Neusaap128/Super-Epische-Audio-Generator/SEAG_F/Core/Inc/main.h

#define ShiftRegFDat_Pin GPIO_PIN_13
#define ShiftRegFDat_GPIO_Port GPIOC
#define ShiftRegFStoClk_Pin GPIO_PIN_14
#define ShiftRegFStoClk_GPIO_Port GPIOC
#define ShiftRegFClk_Pin GPIO_PIN_15
#define ShiftRegFClk_GPIO_Port GPIOC
#define ShiftRegLBarDat_Pin GPIO_PIN_0
#define ShiftRegLBarDat_GPIO_Port GPIOC
#define ShiftRegLBarStoClk_Pin GPIO_PIN_2
#define ShiftRegLBarStoClk_GPIO_Port GPIOC
#define ShiftRegLBarClk_Pin GPIO_PIN_3
#define ShiftRegLBarClk_GPIO_Port GPIOC
#define RotEncoderInA_Pin GPIO_PIN_6
#define RotEncoderInA_GPIO_Port GPIOC
#define RotEncoderInA_EXTI_IRQn EXTI9_5_IRQn
#define RotEncoderInB_Pin GPIO_PIN_7
#define RotEncoderInB_GPIO_Port GPIOC
#define RotEncoderInB_EXTI_IRQn EXTI9_5_IRQn
#define RotEncoderButton_Pin GPIO_PIN_8
#define RotEncoderButton_GPIO_Port GPIOC
#define RotEncoderButton_EXTI_IRQn EXTI9_5_IRQn
#define ToggleInput4_Pin GPIO_PIN_9
#define ToggleInput4_GPIO_Port GPIOA
#define ToggleInput3_Pin GPIO_PIN_10
#define ToggleInput3_GPIO_Port GPIOA
#define ToggleInput2_Pin GPIO_PIN_11
#define ToggleInput2_GPIO_Port GPIOA
#define ToggleInput1_Pin GPIO_PIN_12
#define ToggleInput1_GPIO_Port GPIOA
#define ToggleInput8_Pin GPIO_PIN_15
#define ToggleInput8_GPIO_Port GPIOA
#define ToggleInput7_Pin GPIO_PIN_10
#define ToggleInput7_GPIO_Port GPIOC
#define ToggleInput6_Pin GPIO_PIN_11
#define ToggleInput6_GPIO_Port GPIOC
#define ToggleInput5_Pin GPIO_PIN_12
#define ToggleInput5_GPIO_Port GPIOC
