Neusaap128/Super-Epische-Audio-Generator/SEAG_F/Core/Inc/IO/IO.c

/*
 * IO.c
 *
 *  Created on: Mar 23, 2024
 *      Author: rode-
 */

#define bitset(byte,nbit)   ((byte) |=  (1<<(nbit)))
#define bitclear(byte,nbit) ((byte) &= ~(1<<(nbit)))

#include "IO.h"
#include "RotaryEncoder.h"

//het defineeren van alle pinnen van shift register filter
ShiftRegister_t shiftRegFilterSelect = {
	.clkPort 	 = ShiftRegFClk_GPIO_Port,
	.clkPin   	 = ShiftRegFClk_Pin,
	.dataPort 	 = ShiftRegFDat_GPIO_Port,
	.dataPin  	 = ShiftRegFDat_Pin,
	.enabledPort = ShiftRegFStoClk_GPIO_Port,
	.enabledPin  = ShiftRegFStoClk_Pin
};

//het defineren van alle pinnen voor de ledbar
ShiftRegister_t shiftRegLedbar = {
	.clkPort 	 = ShiftRegLBarClk_GPIO_Port,
	.clkPin   	 = ShiftRegLBarClk_Pin,
	.dataPort 	 = ShiftRegLBarDat_GPIO_Port,
	.dataPin  	 = ShiftRegLBarDat_Pin,
	.enabledPort = ShiftRegLBarStoClk_GPIO_Port,
	.enabledPin  = ShiftRegLBarStoClk_Pin
};
//het defineren van pinnen voor de rotaryEncoder
RotaryEncoder_t rotaryEncoder = {
	.currentPos	= 0,
	.portA   	= RotEncoderInA_GPIO_Port,
	.pinA 	 	= RotEncoderInA_Pin,
	.portB  	= RotEncoderInB_GPIO_Port,
	.pinB 		= RotEncoderInB_Pin,
	.portButton = RotEncoderButton_GPIO_Port,
	.pinButton  = RotEncoderButton_Pin
};


IOState_t IOState;

uint8_t selectedFilter;

// 0 no state transition
// 1, SelectingValue -> Disabled
// 2, Disabled -> SelectingFilter
// 3, SelectingFilter -> SelectingValue
uint8_t switchedStateFlag;

void InitIO(){
	LoadValueIntoShiftRegister(&shiftRegFilterSelect, 0x00);
	ResetShiftRegister(&shiftRegLedbar);
}

void HandleSelectingFilter(){

	selectedFilter = (uint16_t)(rotaryEncoder.currentPos/4) % AMOUNT_OF_FILTERS; //door dat rotery de 4 fase overloopt en 4 keer opteld of afteld moet je delen door 4, voor varable extra dat weergeeft hoeveel filters er zijn
	LoadValueIntoShiftRegister(&shiftRegFilterSelect, 1 << selectedFilter);

}

void HandleSelectingValue(){

	uint8_t led_bar = (rotaryEncoder.currentPos/4); //door dat rotery de 4 fase overloopt en 4 keer opteld of afteld moet je delen door 4
	uint8_t ledbar_array = (1 << led_bar) - 1;		//we werken binair dus hierdoor deze shift opperatie

	changeFilterLevel(getFilters()->filterInstances[selectedFilter], (float)led_bar/(8-1));

	LoadValueIntoShiftRegister(&shiftRegLedbar, ledbar_array);

}

//de functie die moet opgeroepen worden als er op de knop drukt
void ButtonInterrupt(){

	IOState = (IOState + 1)%3;

	rotaryEncoder.currentPos = 0;

	switchedStateFlag = IOState + 1;


}
//op roepen als er aan de knop gedraaid word
void RotaryEncoderInterrupt(){
	rot_intrupt(&rotaryEncoder);
}

uint8_t newSelectedFilters = 0b00000000;
void IOUpdate(){


	uint8_t buttonPressed = HAL_GPIO_ReadPin(ToggleInput1_GPIO_Port, ToggleInput1_Pin);
	if( !buttonPressed) newSelectedFilters |= (1 << 0);  else newSelectedFilters &= ~(1 << 0); // inverted because toggle is upside down
	buttonPressed = HAL_GPIO_ReadPin(ToggleInput2_GPIO_Port, ToggleInput2_Pin);
	if( buttonPressed) newSelectedFilters |= (1 << 1);  else newSelectedFilters &= ~(1 << 1);
	buttonPressed = HAL_GPIO_ReadPin(ToggleInput3_GPIO_Port, ToggleInput3_Pin);
	if( buttonPressed) newSelectedFilters |= (1 << 2);  else newSelectedFilters &= ~(1 << 2);
	buttonPressed = HAL_GPIO_ReadPin(ToggleInput4_GPIO_Port, ToggleInput4_Pin);
	if(!buttonPressed) newSelectedFilters |= (1 << 3);  else newSelectedFilters &= ~(1 << 3); // inverted because toggle is upside down
	buttonPressed = HAL_GPIO_ReadPin(ToggleInput5_GPIO_Port, ToggleInput5_Pin);
	if( buttonPressed) newSelectedFilters |= (1 << 4);  else newSelectedFilters &= ~(1 << 4);



	/*
	uint8_t buttonPressed = HAL_GPIO_ReadPin(ToggleInput6_GPIO_Port, ToggleInput6_Pin);
	SetFilterState(5, buttonPressed);
	uint8_t buttonPressed = HAL_GPIO_ReadPin(ToggleInput7_GPIO_Port, ToggleInput7_Pin);
	SetFilterState(6, buttonPressed);
	uint8_t buttonPressed = HAL_GPIO_ReadPin(ToggleInput8_GPIO_Port, ToggleInput8_Pin);
	SetFilterState(7, buttonPressed);
	 */

	if(newSelectedFilters != GetEnabledFilters()){
		UpdateLedsActiveFilters();
	}

	//Handling Transistions
	if(switchedStateFlag > 0){

		switch(switchedStateFlag){
			case 1:
				LoadValueIntoShiftRegister(&shiftRegFilterSelect, GetEnabledFilters());
				ResetShiftRegister(&shiftRegLedbar);
				break;
			case 2:
				// Nothing needs to be reset
				break;
			case 3:
				// Nothing needs to be reset
				rotaryEncoder.currentPos = 4; // At least one led on, at start
				break;
		}

		switchedStateFlag = 0;

	}

	//Handling states
	switch (IOState) {
	    case Disabled:
	    	break;
	    case SelectingFilter:			//deze fase gaat er een filter dat je wilt aanpassen geselecteerd
	    	HandleSelectingFilter();
	    	break;
	    case SelectingValue:			//hier ga je van de geselecteerde filter de waarde gaan aanpassen
	    	HandleSelectingValue();
	    	break;
	  }

}

void UpdateLedsActiveFilters(){

	SetFilterStates(newSelectedFilters);
	LoadValueIntoShiftRegister(&shiftRegFilterSelect, GetEnabledFilters());

}
