Neusaap128/Super-Epische-Audio-Generator/CubeIDEProject/Core/Inc/DSP/DSP.h

/*
 * DSP.h
 *
 *  Created on: Feb 25, 2024
 *      Author: Joran
 */

#ifndef INC_DSP_DSP_H_
#define INC_DSP_DSP_H_

#define AMOUNT_OF_FILTERS 4

#include "stm32g4xx_hal.h"
#include <string.h>
#include <stdio.h>
#include <stdint.h>
#include <stdlib.h>
#include "../Filters/MovingAverage.h"

typedef uint32_t SampleType;

extern const int N;
extern const int samplingRate;

void InitDSP();
void AppendSample(SampleType sample);
//void TimerCallback(ADC_HandleTypeDef* hadc1, UART_HandleTypeDef* hlpuart1, DAC_HandleTypeDef* hdac1);
void ApplyFilters();


#endif /* INC_DSP_DSP_H_ */
