Neusaap128/Super-Epische-Audio-Generator/SEAG_F/Core/Inc/Common.h

/*
 * Common.h
 *
 *  Created on: May 13, 2024
 *      Author: Joran
 */

#ifndef INC_COMMON_H_
#define INC_COMMON_H_

#include <stdint.h>

#define AMOUNT_OF_FILTERS 5 //Hoeveelheid filters die aanwezig zijn

typedef int16_t SampleType;	//datatype van 1 audio sample

#endif /* INC_COMMON_H_ */
