Neusaap128/Super-Epische-Audio-Generator/FiltersWavFiles/code/Reverb.c

#include "Reverb.h"

//Order delayS smallest to largest
Reverb* initializeReverb(uint32_t sampleRate, uint8_t amountOfCombFilters, float *delayCombS, uint8_t amountOfAllPassFilters, float *delayAllS){

    Reverb *reverb = malloc(sizeof(Reverb));


    //Comb
    reverb->amountOfCombFilters = amountOfCombFilters;

    reverb->combFilters = malloc(reverb->amountOfCombFilters*sizeof(CombFeedforward));

    for(int i = 0; i < reverb->amountOfCombFilters; i++){
        reverb->combFilters[i] = initializeCombFeedback(sampleRate, delayCombS[i], 1.0f, 0.8f);
    }
    
    
    //AllPass
    reverb->amountOfAllPassFilters = amountOfAllPassFilters;
    reverb->allPassFilters = malloc(reverb->amountOfAllPassFilters*sizeof(AllPass));

    for(int i = 0; i < reverb->amountOfAllPassFilters; i++){
        reverb->allPassFilters[i] = initializeAllPass(sampleRate, delayAllS[i], 1, 0.8f);
    }

    return reverb;

}

SampleType reverbAppendSample(Reverb* reverb, SampleType newSample){

	SampleType combSumOutput = 0;

    for(int i = 0; i < reverb->amountOfCombFilters; i++){
        combSumOutput += combFeedbackAppendSample(reverb->combFilters[i], newSample)/reverb->amountOfCombFilters;
    }


    SampleType  previousAllPassOutput = combSumOutput;

    for (int i = 0; i < reverb->amountOfAllPassFilters; i++){
        previousAllPassOutput = allPassAppendSample(reverb->allPassFilters[i], previousAllPassOutput);
    }
    
    return previousAllPassOutput;

}

void setReverbLevel(Reverb* reverb, float a){

	for(uint8_t i = 0; i < reverb->amountOfCombFilters; i++){
		setCombFeedbackLevel(reverb->combFilters[i], a);
	}

	for(uint8_t i = 0; i < reverb->amountOfAllPassFilters; i++){
		setAllPassLevel(reverb->allPassFilters[i], a);
	}

}
